rasteri/HIDman/firmware/usbll.c

#include <stdio.h>
#include <stdlib.h>
#include "type.h"
#include "ch559.h"
#include "system.h"
#include "defs.h"
#include "usbdef.h"
#include "usbhost.h"
#include "menu.h"
#include "data.h"
#include "settings.h"
#include "andyalloc.h"
#include "keyboardled.h"
#include "parsedescriptor.h"
#include "ps2protocol.h"
#include "usbll.h"

__at(0x0000) unsigned char __xdata RxBuffer[MAX_PACKET_SIZE];
__at(0x0100) unsigned char __xdata TxBuffer[MAX_PACKET_SIZE];

//root hub port
//USB_HUB_PORT __xdata RootHubPort[ROOT_HUB_PORT_NUM];

//sub hub port - should be dynamically allocated
//USB_HUB_PORT __xdata SubHubPort[ROOT_HUB_PORT_NUM][MAX_EXHUB_PORT_NUM];

__xdata LinkedList* PolledDevices = NULL;

UINT8 EnableRootHubPort(UINT8 rootHubIndex, UINT8 * DeviceSpeed)
{
	if (rootHubIndex == 0)
	{
		if (USB_HUB_ST & bUHS_H0_ATTACH)
		{
			if ((UHUB0_CTRL & bUH_PORT_EN) == 0x00)
			{
				if (USB_HUB_ST & bUHS_DM_LEVEL)
				{
					*DeviceSpeed = LOW_SPEED;

					TRACE("low speed device on hub 0\r\n");
				}
				else
				{
					*DeviceSpeed = FULL_SPEED;

					TRACE("full speed device on hub 0\r\n");
				}

				if (*DeviceSpeed == LOW_SPEED)
				{
					UHUB0_CTRL |= bUH_LOW_SPEED;
				}
			}

			UHUB0_CTRL |= bUH_PORT_EN;

			return ERR_SUCCESS;
		}
	}
	else if (rootHubIndex == 1)
	{
		if (USB_HUB_ST & bUHS_H1_ATTACH)
		{
			if ((UHUB1_CTRL & bUH_PORT_EN) == 0x00)
			{
				if (USB_HUB_ST & bUHS_HM_LEVEL)
				{
					*DeviceSpeed = LOW_SPEED;

					TRACE("low speed device on hub 1\r\n");
				}
				else
				{
					*DeviceSpeed = FULL_SPEED;

					TRACE("full speed device on hub 1\r\n");
				}

				if (*DeviceSpeed == LOW_SPEED)
				{
					UHUB1_CTRL |= bUH_LOW_SPEED;
				}
			}

			UHUB1_CTRL |= bUH_PORT_EN;

			return ERR_SUCCESS;
		}
	}

	return ERR_USB_DISCON;
}

void DisableRootHubPort(UINT8 RootHubIndex)
{

	if (RootHubIndex == 0)
	{
		UHUB0_CTRL = 0x00;
	}
	else if (RootHubIndex == 1)
	{
		UHUB1_CTRL = 0x00;
	}
}



void SetHostUsbAddr(UINT8 addr)
{
	USB_DEV_AD = USB_DEV_AD & bUDA_GP_BIT | addr & 0x7F;
}

void SetUsbSpeed(UINT8 FullSpeed) // set current speed
{
	if (FullSpeed)
	{
		USB_CTRL &= ~bUC_LOW_SPEED;
		UH_SETUP &= ~bUH_PRE_PID_EN;
	}
	else
	{
		USB_CTRL |= bUC_LOW_SPEED;
	}
}

void ResetRootHubPort(UINT8 RootHubIndex)
{
	SetHostUsbAddr(0x00);
	SetUsbSpeed(1);

	if (RootHubIndex == 0)
	{
		UHUB0_CTRL = UHUB0_CTRL & ~bUH_LOW_SPEED | bUH_BUS_RESET; 
		mDelaymS(25);											  
		UHUB0_CTRL = UHUB0_CTRL & ~bUH_BUS_RESET;				  
	}
	else if (RootHubIndex == 1)
	{
		UHUB1_CTRL = UHUB1_CTRL & ~bUH_LOW_SPEED | bUH_BUS_RESET; 
		mDelaymS(25);											  
		UHUB1_CTRL = UHUB1_CTRL & ~bUH_BUS_RESET;				  
	}

	mDelayuS(250);
	UIF_DETECT = 0;
}

void SelectHubPort(USB_HUB_PORT *pUsbDevice)
{
	if (pUsbDevice->IsRootHub)
	{
		// normal device
		SetHostUsbAddr(pUsbDevice->DeviceAddress);
		SetUsbSpeed(pUsbDevice->DeviceSpeed);
	}
	else
	{
		SetHostUsbAddr(pUsbDevice->DeviceAddress);
		if (pUsbDevice->DeviceSpeed == LOW_SPEED)
		{
			UH_SETUP |= bUH_PRE_PID_EN;
		}
		SetUsbSpeed(pUsbDevice->DeviceSpeed);
	}
}

/*void SelectHubPort(UINT8 RootHubIndex, UINT8 HubPortIndex)
{
	if (HubPortIndex == EXHUB_PORT_NONE)
	{
		//normal device
		SetHostUsbAddr(RootHubPort[RootHubIndex].DeviceAddress);
		SetUsbSpeed(RootHubPort[RootHubIndex].DeviceSpeed);
	}
	else
	{
		USB_HUB_PORT *pUsbDevice = &SubHubPort[RootHubIndex][HubPortIndex];
		SetHostUsbAddr(pUsbDevice->DeviceAddress);
		if (pUsbDevice->DeviceSpeed == LOW_SPEED)
		{
			UH_SETUP |= bUH_PRE_PID_EN;
		}

		SetUsbSpeed(pUsbDevice->DeviceSpeed);
	}
}*/

void InitUsbHost(void)
{
	UINT8 i;
	IE_USB = 0;

	USB_CTRL = bUC_HOST_MODE;
	USB_DEV_AD = 0x00;
	UH_EP_MOD = bUH_EP_TX_EN | bUH_EP_RX_EN;
	UH_RX_DMA = 0x0000;
	UH_TX_DMA = 0x0001;
	UH_RX_CTRL = 0x00;
	UH_TX_CTRL = 0x00;

	UHUB1_CTRL &= ~bUH1_DISABLE; //enable root hub1

	USB_CTRL = bUC_HOST_MODE | bUC_INT_BUSY | bUC_DMA_EN;

	UH_SETUP = bUH_SOF_EN;
	USB_INT_FG = 0xFF;
	for (i = 0; i < 2; i++)
	{
		DisableRootHubPort(i);
	}
	USB_INT_EN = bUIE_TRANSFER | bUIE_DETECT;
}

UINT8   USBHostTransact( UINT8 endp_pid, UINT8 tog, UINT16 timeout )
{
    UINT8   TransRetry;
    UINT8   s, r;
    UINT16  i;
    UH_RX_CTRL = tog;
    UH_TX_CTRL =tog ;
    TransRetry = 0;
    do
    {
        UH_EP_PID = endp_pid;                                    // 指定令牌PID和目的端点号
        UIF_TRANSFER = 0;                                        // 允许传输

        for ( i = WAIT_USB_TOUT_200US; i != 0 && UIF_TRANSFER == 0; i -- )
        {
            ;
        }
        UH_EP_PID = 0x00;                                        // 停止USB传输

        if ( UIF_TRANSFER == 0 )
        {
            return( ERR_USB_UNKNOWN );
        }

        if ( UIF_TRANSFER )                                      // 传输完成
        {
            if ( U_TOG_OK )
            {
                return( ERR_SUCCESS );
            }
            r = USB_INT_ST & MASK_UIS_H_RES;                     // USB设备应答状态
            if ( r == USB_PID_STALL )
            {
                //printf("USB_PID_STALL\n");
                return( r | ERR_USB_TRANSFER );
            }
            if ( r == USB_PID_NAK )
            {
                if ( timeout == 0 )
                {
                    //printf("USB_PID_NAK timeout\n");
                    return( r | ERR_USB_TRANSFER );
                }
                if ( timeout < 0xFFFF )
                {
                    timeout --;
                }
                -- TransRetry;
            }
            else switch ( endp_pid >> 4 )
                {
                case USB_PID_SETUP:
                case USB_PID_OUT:
                    if ( U_TOG_OK )
                    {
                        return( ERR_SUCCESS );
                    }
                    if ( r == USB_PID_ACK )
                    {
                        return( ERR_SUCCESS );
                    }
                    if ( r == USB_PID_STALL || r == USB_PID_NAK )
                    {
                        //printf("USB PID OUT : USB_PID_STALL or USB_PID_NAK timeout %x\n", r);
                        return( r | ERR_USB_TRANSFER );
                    }
                    if ( r )
                    {
                        //printf("USB PID OUT : ERR_USB_TRANSFER unexpected answer %x\n", r);
                        return( r | ERR_USB_TRANSFER );          // Not a timeout/error, unexpected answer
                    }
                    break;                                       // 超时重试
                case USB_PID_IN:
                    if ( U_TOG_OK )
                    {
                        return( ERR_SUCCESS );
                    }
                    if ( tog ? r == USB_PID_DATA1 : r == USB_PID_DATA0 )
                    {
                        return( ERR_SUCCESS );
                    }
                    if ( r == USB_PID_STALL || r == USB_PID_NAK )
                    {
                        //printf("USB_PID_IN : USB_PID_STALL or USB_PID_NAK%x\n", r);
                        return( r | ERR_USB_TRANSFER );
                    }
                    if ( r == USB_PID_DATA0 && r == USB_PID_DATA1 )// 不同步则需丢弃后重试
                    {
                    }                                            // 不同步重试
                    else if ( r )
                    {
                        //printf("USB_PID_IN : ERR_USB_TRANSFER unexpected answer %x\n", r);
                        return( r | ERR_USB_TRANSFER );          // 不是超时/出错,意外应答
                    }
                    break;                                       // 超时重试
                default:
                    //printf("unknown err\n");
                    return( ERR_USB_UNKNOWN );                   // 不可能的情况
                    break;
                }
        }
        else                                                     // 其它中断,不应该发生的情况
        {
            USB_INT_FG = 0xFF;                                   //清中断标志
        }
        mDelayuS( 15 );
    }
    while ( ++ TransRetry < 3 );
    return( ERR_USB_TRANSFER );                                  // 应答超时
}


UINT8 HostCtrlTransfer(USB_SETUP_REQ *pSetupReq, UINT8 MaxPacketSize0, PUINT8 DataBuf, PUINT16 RetLen)
{
	UINT16 RemLen = 0;
	UINT8 s, RxLen, RxCnt, TxCnt;
	PUINT8 pBuf;
	PUINT16 pLen;

	pBuf = DataBuf;
	pLen = RetLen;
	mDelayuS(200);
	if (pLen)
	{
		*pLen = 0;
	}

	for (TxCnt = 0; TxCnt < sizeof(USB_SETUP_REQ); TxCnt++)
	{
		TxBuffer[TxCnt] = ((UINT8 *)pSetupReq)[TxCnt];
	}

	UH_TX_LEN = sizeof(USB_SETUP_REQ);

	s = USBHostTransact(USB_PID_SETUP << 4, 0x00, 10000);
	if (s != ERR_SUCCESS)
	{
		TRACE1("quit at line %d\r\n", (UINT16)__LINE__);

		return (s);
	}
	UH_RX_CTRL = UH_TX_CTRL = bUH_R_TOG | bUH_R_AUTO_TOG | bUH_T_TOG | bUH_T_AUTO_TOG;
	UH_TX_LEN = 0x01;
	RemLen = (pSetupReq->wLengthH << 8) | (pSetupReq->wLengthL);
	if (RemLen && pBuf)
	{
		if (pSetupReq->bRequestType & USB_REQ_TYP_IN)
		{
			while (RemLen)
			{
				mDelayuS(200);
				s = USBHostTransact(USB_PID_IN << 4, UH_RX_CTRL, 10000);
				if (s != ERR_SUCCESS)
				{
					TRACE1("quit at line %d\r\n", (UINT16)__LINE__);

					return (s);
				}
				RxLen = USB_RX_LEN < RemLen ? USB_RX_LEN : RemLen;
				RemLen -= RxLen;
				if (pLen)
				{
					*pLen += RxLen;
				}

				for (RxCnt = 0; RxCnt != RxLen; RxCnt++)
				{
					*pBuf = RxBuffer[RxCnt];
					pBuf++;
				}
				if (USB_RX_LEN == 0 || (USB_RX_LEN < MaxPacketSize0))
				{
					break;
				}
			}
			UH_TX_LEN = 0x00;
		}
		else
		{
			while (RemLen)
			{
				mDelayuS(200);
				UH_TX_LEN = RemLen >= MaxPacketSize0 ? MaxPacketSize0 : RemLen;

				for (TxCnt = 0; TxCnt != UH_TX_LEN; TxCnt++)
				{
					TxBuffer[TxCnt] = *pBuf;
					pBuf++;
				}
				s = USBHostTransact(USB_PID_OUT << 4 | 0x00, UH_TX_CTRL, 200000 / 20);
				if (s != ERR_SUCCESS)
				{
					TRACE1("quit at line %d\r\n", (UINT16)__LINE__);

					return (s);
				}
				RemLen -= UH_TX_LEN;
				if (pLen)
				{
					*pLen += UH_TX_LEN;
				}
			}


		}
	}

	mDelayuS(200);
	s = USBHostTransact((UH_TX_LEN ? USB_PID_IN << 4 | 0x00 : USB_PID_OUT << 4 | 0x00), bUH_R_TOG | bUH_T_TOG, 200000 / 20);
	if (s != ERR_SUCCESS)
	{
		TRACE1("quit at line %d\r\n", (UINT16)__LINE__);

		return (s);
	}
	if (UH_TX_LEN == 0)
	{
		return (ERR_SUCCESS); // ״̬OUT
	}
	if (USB_RX_LEN == 0)
	{
		return (ERR_SUCCESS);
	}
	return (ERR_USB_BUF_OVER);
}

UINT8 TransferReceive(ENDPOINT *pEndPoint, UINT8 *pData, UINT16 *pRetLen, UINT16 timeout)
{
	UINT8 s;
	UINT8 len;

	s = USBHostTransact(USB_PID_IN << 4 | (pEndPoint->EndpointAddr & 0x7F), pEndPoint->TOG ? bUH_R_TOG | bUH_T_TOG : 0, timeout);
	if (s == ERR_SUCCESS)
	{
		UINT8 i;
		len = USB_RX_LEN;

		for (i = 0; i < len; i++)
		{
			*pData++ = RxBuffer[i];
		}

		if (pRetLen != NULL)
		{
			*pRetLen = len;
		}

		pEndPoint->TOG = pEndPoint->TOG ? FALSE : TRUE;
	}

	return (s);
}

UINT8 TransferSend(ENDPOINT *pEndPoint, UINT8 *pData, UINT8 len, UINT16 timeout)
{
	UINT8 s;
	UINT8 i;

	// Copy data to transmit buffer
	for (i = 0; i < len; i++)
	{
		TxBuffer[i] = pData[i];
	}
	UH_TX_LEN = len;

	s = USBHostTransact(USB_PID_OUT << 4 | (pEndPoint->EndpointAddr & 0x7F), pEndPoint->TOG ? bUH_R_TOG | bUH_T_TOG : 0, timeout);
	if (s == ERR_SUCCESS)
	{
		pEndPoint->TOG = pEndPoint->TOG ? FALSE : TRUE;
	}

	return (s);
}
