rasteri/HIDman/firmware/inc/usbhost.h

#ifndef _USBHOST_H_
#define _USBHOST_H_

#include <stdbool.h>
#include "defs.h"
#include "linkedlist.h"


#define ERR_SUCCESS         0x00
#define ERR_USB_CONNECT     0x15
#define ERR_USB_DISCON      0x16
#define ERR_USB_BUF_OVER    0x17
#define ERR_USB_DISK_ERR    0x1F
#define ERR_USB_TRANSFER    0x20
#define ERR_USB_UNSUPPORT   0xFB
#define ERR_USB_UNKNOWN     0xFE





#ifndef	USB_INT_RET_ACK
#define	USB_INT_RET_ACK		     USB_PID_ACK
#define	USB_INT_RET_NAK		     USB_PID_NAK
#define	USB_INT_RET_STALL	     USB_PID_STALL
#define	USB_INT_RET_DATA0	     USB_PID_DATA0
#define	USB_INT_RET_DATA1	     USB_PID_DATA1
#define	USB_INT_RET_TOUT	     0x00
#define	USB_INT_RET_TOUT1	     0x04
#define	USB_INT_RET_TOUT2	     0x08
#define	USB_INT_RET_TOUT3	     0x0C
#endif

//number of root hub ports
#define ROOT_HUB_PORT_NUM      2

//maximum number of external hub ports
#define MAX_EXHUB_PORT_NUM     4

//none external hub port
#define EXHUB_PORT_NONE        0xff

//maximum number of interfaces per devicve
#define MAX_INTERFACE_NUM      4
//maximum number of interfaces across all devices
#define MAX_GLOBAL_INTERFACE_NUM      12
//maximum number of endpoints per interface
#define MAX_ENDPOINT_NUM       4
//maximum level of external hub
#define MAX_EXHUB_LEVEL        1

//in 
#define ENDPOINT_OUT           0
//out
#define ENDPOINT_IN            1

//endpoint struct
typedef struct _ENDPOINT
{
	UINT8 EndpointAddr;
	UINT16 MaxPacketSize;
	
	UINT8 EndpointDir : 1;
	UINT8 TOG : 1;
} ENDPOINT, *PENDPOINT;

//hid report define
#define HID_LOCAL_ITEM_TAG_USAGE         0x00

#define HID_GLOBAL_ITEM_TAG_USAGE_PAGE       0x00
#define HID_GLOBAL_ITEM_TAG_LOGICAL_MINIMUM  0x01
#define HID_GLOBAL_ITEM_TAG_LOGICAL_MAXIMUM  0x02
#define HID_GLOBAL_ITEM_TAG_PHYSICAL_MINIMUM 0x03
#define HID_GLOBAL_ITEM_TAG_PHYSICAL_MAXIMUM 0x04
#define HID_GLOBAL_ITEM_TAG_REPORT_SIZE      0x07
#define HID_GLOBAL_ITEM_TAG_REPORT_ID        0x08
#define HID_GLOBAL_ITEM_TAG_REPORT_COUNT     0x09

#define HID_MAIN_ITEM_TAG_INPUT          0x08

#define TYPE_MAIN         0
#define TYPE_GLOBAL       1
#define TYPE_LOCAL        2

#define HID_ITEM_FORMAT_SHORT      0
#define HID_ITEM_FORMAT_LONG       1

#define HID_ITEM_TAG_LONG          15

//usage page
#define USAGE_PAGE_NONE            0x00
#define USAGE_PAGE_GENERIC_DESKTOP 0x01
#define USAGE_PAGE_KEYBOARD        0x07
#define USAGE_PAGE_BUTTON          0x09

//usage
#define USAGE_NONE         0x00
#define USAGE_X            0x30
#define USAGE_Y            0x31
#define USAGE_WHEEL        0x38

extern UINT8 sInterfacePoolPos;

typedef struct _HID_ITEM_INFO
{
	unsigned int format;
	UINT8 size;
	UINT8 type;
	UINT8 tag;

	union
	{
		UINT8  u8;
		INT8   s8;
		UINT16 u16;
		INT16  s16;
		UINT32 u32;
		INT32  s32;

		const UINT8 *longdata;
	} value;
	
} HID_ITEM;


//hid segement define
#define HID_SEG_KEYBOARD_MODIFIER_INDEX  0
#define HID_SEG_KEYBOARD_VAL_INDEX       1

#define HID_SEG_BUTTON_INDEX             2
#define HID_SEG_X_INDEX                  3
#define HID_SEG_Y_INDEX                  4
#define HID_SEG_WHEEL_INDEX              5

#define HID_SEG_NUM                      6

#define MAX_USAGE_NUM      10

#define MAX_REPORTS 18

//interface struct
typedef struct _INTERFACE
{
	UINT8     InterfaceClass;
	UINT8	  InterfaceSubClass;
	UINT8     InterfaceProtocol;

	UINT16    ReportSize;
	
	UINT8     EndpointNum;   //number of endpoints in this interface
	ENDPOINT  Endpoint[MAX_ENDPOINT_NUM]; //endpoints
	
	bool usesReports;
	__xdata LinkedList *Reports;

} INTERFACE, *PINTERFACE;
void InitInterface(INTERFACE* Interface);

//hub struct
#define  PORT_DEVICE_NONE         0
#define  PORT_DEVICE_INSERT       1
#define  PORT_DEVICE_ENUM_FAILED  2
#define  PORT_DEVICE_ENUM_SUCCESS 3

// This is actually more like a "device on hub port" than a port itself
typedef struct _USB_HUB_PORT
{
	// Port status
	UINT8		HubPortStatus;
	UINT8       HubPortNum;

	// Device Status
	UINT8       DeviceClass;
	UINT8       MaxPacketSize0;
	
	UINT16      VendorID;
	UINT16      ProductID;
/* this isn't needed
	UINT16      bcdDevice;
*/

	UINT8       DeviceAddress;
	UINT8       DeviceSpeed;
	UINT8       InterfaceNum;

	__xdata LinkedList* Interfaces;
	
	//not sure we need this or the next one
	// which root hub this device is attached to
	UINT8		RootHubNum;

	// whether or not this device is directly connected to root
	UINT8		IsRootHub;

	// Logitech Fn swap configured successfully
	UINT8		LogitechConfigured;
	// keyboard sent a keypress (awake); config should run from the main loop, not the poll path
	UINT8		LogitechWoke;
	// Logitech device slot that has keyboard (1-6), 0 if unknown
	UINT8		LogitechDevNum;
	// Logitech FN_INVERSION feature index, 0 if not discovered
	UINT8		LogitechFnFeatureIndex;

} USB_HUB_PORT, *USB_PHUB_PORT;

#define  LOW_SPEED      0
#define  FULL_SPEED     1


extern void InitUsbHost(void);
extern void InitUsbData(void);
extern void DealUsbPort(void);
extern void InterruptProcessRootHubPort(UINT8 port_index);
extern void UpdateUsbKeyboardLed(UINT8 led);
extern INTERFACE* AllocInterface(UINT8 count);
void ReenumerateAllPorts(void);

// Apply the Logitech Fn-swap setting to connected Unifying keyboards in place
void ReapplyLogitechFnSwap(void);

void ProcessUsbHostPort(void);

extern __xdata  BOOL volatile s_CheckUsbPort0;
extern __xdata  BOOL volatile s_CheckUsbPort1;

// USB specific traces

#if 0
#include <stdio.h>
#define TRACE(x)  printf(x)
#define TRACE1(fmt, x)  printf(fmt, x)
#define TRACE2(fmt, x1, x2) printf(fmt, x1, x2)
#define TRACE3(fmt, x1, x2, x3) printf(fmt, x1, x2, x3)

#else
#define TRACE(x)  
#define TRACE1(fmt, x)  
#define TRACE2(fmt, x1, x2)
#define TRACE3(fmt, x1, x2, x3)
#endif

#endif
