rasteri/HIDman/firmware/xt.c

#include <stdint.h>
#include <stdbool.h>
#include <stdio.h>
#include <string.h>
#include "ch559.h"
#include "usbhost.h"
#include "uart.h"
#include "ps2.h"
#include "data.h"
#include "ps2protocol.h"
#include "defs.h"
#include "xt.h"
#include "scancode.h"

__xdata uint16_t ratelimit = 0;

__xdata uint8_t oldstate = 0;
void XTProcessPort(void)
{
	const uint8_t *chunk;
	static __data uint8_t sb;

	bool reEnter = 0;

	do
	{
		/*if (ports[PORT_KEY].state != oldstate)
		{
			printf("%hhd-%hhd\n", ports[PORT_KEY].state, ports[PORT_KEY].sendbit);
			oldstate = ports[PORT_KEY].state;
		}*/
		sb = ports[PORT_KEY].sendbit;
		reEnter = 0;

		// XT bit-bang state machine
		switch (ports[PORT_KEY].state)
		{
		case S_INIT:
			ports[PORT_KEY].state = S_IDLE;
			reEnter = 1;
			ports[PORT_KEY].sendbit = 0;
			WritePS2Clock(PORT_KEY, 1);
			break;

		case S_IDLE:
			// if host is not inhibiting (i.e. not pulling clock low)
			if (ReadPS2Clock(PORT_KEY))
			{
				if (ports[PORT_KEY].rateLimit > 0) ports[PORT_KEY].rateLimit--;

				//if ratelimiter is ok and buffer not empty
				if (ports[PORT_KEY].rateLimit == 0 && ports[PORT_KEY].sendBuffEnd != ports[PORT_KEY].sendBuffStart)
				{

					ports[PORT_KEY].rateLimit = XT_RATE_LIMIT;

					chunk = ports[PORT_KEY].sendBuff.chunky[ports[PORT_KEY].sendBuffStart];
					ports[PORT_KEY].data = chunk[ports[PORT_KEY].bytenum + 1];
					//DEBUG_OUT("Consuming %x %x %x %x\n", ports[PORT_KEY].sendBuffStart, ports[PORT_KEY].sendBuffEnd, chunk[0], ports[PORT_KEY].data);

					// if data line is already high, we can go straight to sending data
					if (ReadPS2Data(PORT_KEY))
					{

						// Go to S_SEND_CLOCK_LOW even though we're technically high, as this will make sure counters are right etc
						// we could just jump straight to S_SEND_CLOCK_FALLING but better to keep logic consistent
						ports[PORT_KEY].state = S_SEND_CLOCK_LOW;
						ports[PORT_KEY].recvbit = 0;
						//reEnter = 1;
					}
					// otherwise, have to send an RTS first
					else
					{
						// make clock line low, then wait for CTS (data high)
						WritePS2Clock(PORT_KEY, 0);
						ports[PORT_KEY].state = S_WAITING_CTS;
						ports[PORT_KEY].recvbit = 0;
					}
				}

				ports[PORT_KEY].resetCounter = 0;
			}

			// host is inhibiting (pulling clock low)
			// wait 20ms then send self-test byte
			else {
				ports[PORT_KEY].resetCounter++;
				if (ports[PORT_KEY].resetCounter == 1200){
					SimonSaysSendKeyboard(KEY_BATCOMPLETE);
				}
			}

			break;

		case S_WAITING_CTS:

			ports[PORT_KEY].recvbit++;

			// wait 112us before doing anything
			if (ports[PORT_KEY].recvbit >= 6)
			{
				if (ReadPS2Data(PORT_KEY))
				{
					ports[PORT_KEY].state = S_SEND_CLOCK_LOW;

					// reuse recvbit as counter
					ports[PORT_KEY].recvbit = 0;
				}
			}
			else
			{
				// timeout waiting for CTS after 250us, go back to idle
				if (ports[PORT_KEY].recvbit >= 16)
				{
					WritePS2Clock(PORT_KEY, 1);
					WritePS2Data(PORT_KEY, 1);
					ports[PORT_KEY].recvbit = 0;
					ports[PORT_KEY].resetCounter = 0;
					ports[PORT_KEY].state = S_IDLE;
				}
			}
			break;

		case S_SEND_CLOCK_LOW:
			// reuse recvbit as counter
			ports[PORT_KEY].recvbit++;

			// we want to set the data in the middle of the low cycle
			if (ports[PORT_KEY].recvbit == 2)
			{

				// bit 0 is start bit (high)
				if (sb == 0)
				{
					WritePS2Data(PORT_KEY, 1);
				}

				// bits 1-8 are data bits
				else if (sb > 0 && sb < 9)
				{
					// set current bit data
					WritePS2Data(PORT_KEY, ports[PORT_KEY].data & 0x01);

					// shift in preperation for next bit
					ports[PORT_KEY].data = ports[PORT_KEY].data >> 1;
				}

				ports[PORT_KEY].sendbit++;
				ports[PORT_KEY].state = S_SEND_CLOCK_RISE;
				ports[PORT_KEY].recvbit = 0;

				//make clock high
				WritePS2Clock(PORT_KEY, 1);
			}
			/*else
			{
				ports[PORT_KEY].state = S_SEND_CLOCK_RISE;
				ports[PORT_KEY].recvbit = 0;
			}*/
			break;

		case S_SEND_CLOCK_RISE:
			ports[PORT_KEY].recvbit++;

			// first time round, set clock high
			if (ports[PORT_KEY].recvbit == 1)
			{
				//make clock high
				WritePS2Clock(PORT_KEY, 1);
			}
			// wait 6 clock cycles (100us) before the next thing
			else if (ports[PORT_KEY].recvbit >= 2)
			{
				ports[PORT_KEY].state = S_SEND_CLOCK_HIGH;
			}

			break;

		case S_SEND_CLOCK_HIGH:

			// if final bit, move onto next byte
			if (sb == 10)
			{
				ports[PORT_KEY].sendbit = 0;

				// for keyboard get the next byte in the chunk
				chunk = ports[PORT_KEY].sendBuff.chunky[ports[PORT_KEY].sendBuffStart];

				ports[PORT_KEY].bytenum++;

				// if we've run out of bytes in this chunk
				if (ports[PORT_KEY].bytenum == chunk[0])
				{
					// move onto next chunk
					//DEBUG_OUT("Consumed %x %x\n", ports[PORT_KEY].sendBuffStart, ports[PORT_KEY].sendBuffEnd);
					ports[PORT_KEY].sendBuffStart = (ports[PORT_KEY].sendBuffStart + 1) & 0x3F;
					ports[PORT_KEY].bytenum = 0;
				}
				else
				{
					ports[PORT_KEY].data = chunk[ports[PORT_KEY].bytenum + 1];
				}

				// also need to set data line high
				WritePS2Data(PORT_KEY, 1);

				// give ourselves a little break between bytes
				ports[PORT_KEY].state = S_IDLE;
				ports[PORT_KEY].resetCounter = 0;
			}
			else
			{
				ports[PORT_KEY].state = S_SEND_CLOCK_FALL;
			}
			break;

		// data has been set, send falling edge of clock
		case S_SEND_CLOCK_FALL:

			WritePS2Clock(PORT_KEY, 0);
			ports[PORT_KEY].state = S_SEND_CLOCK_LOW;
			ports[PORT_KEY].recvbit = 0;
			break;
		}
	} while (reEnter);
}
