rasteri/HIDman/firmware/inc/scancode.h

#ifndef __SCANCODES_H__
#define __SCANCODES_H__
#include <stdbool.h>
#include <stdint.h>

extern __code uint8_t KEY_ACK[];
extern __code uint8_t KEY_BATCOMPLETE[];
extern __code uint8_t KEY_ID[];

extern __code uint8_t MOUSE_ACK[];
extern __code uint8_t MOUSE_BATCOMPLETE[];
extern __code uint8_t MOUSE_ID[];

extern __code uint8_t KEY_LEFT_BREAK[];
extern __code uint8_t KEY_RIGHT_BREAK[];
extern __code uint8_t KEY_UP_BREAK[];
extern __code uint8_t KEY_DOWN_BREAK[];

extern __code uint8_t KEY_LEFT_MAKE[];
extern __code uint8_t KEY_RIGHT_MAKE[];
extern __code uint8_t KEY_UP_MAKE[];
extern __code uint8_t KEY_DOWN_MAKE[];

extern __code uint8_t KEY_LCTRL_MAKE[];
extern __code uint8_t KEY_LALT_MAKE[];
extern __code uint8_t KEY_SPACE_MAKE[];
extern __code uint8_t KEY_ENTER_MAKE[];

extern __code uint8_t KEY_LCTRL_BREAK[];
extern __code uint8_t KEY_LALT_BREAK[];
extern __code uint8_t KEY_SPACE_BREAK[];
extern __code uint8_t KEY_ENTER_BREAK[];

extern __code uint8_t KEY_SCANCODE_2[];
extern __code uint8_t KEY_ECHO[];
extern __code uint8_t KEY_ERROR[];

extern __code uint8_t KEY_SET1_LSHIFT_MAKE[];
extern __code uint8_t KEY_SET1_LSHIFT_BREAK[];

extern __code uint8_t KEY_SET2_LSHIFT_MAKE[];
extern __code uint8_t KEY_SET2_LSHIFT_BREAK[];

extern __code uint8_t * __code HIDtoSET2_Make[];
extern __code uint8_t * __code HIDtoSET2_Break[];

extern __code uint8_t * __code HIDtoSET1_Make[];
extern __code uint8_t * __code HIDtoSET1_Break[];

extern __code uint8_t KEY_SET2_WWWREFRESH_MAKE[];
extern __code uint8_t KEY_SET2_WWWREFRESH_BREAK[];

#endif //__SCANCODES_H__
