rasteri/HIDman/firmware/andyalloc.c

/*
    andyalloc.c

    Trivial allocator that just chucks everything on a heap in order
    Can't free, all memory must be wiped and re-filled
*/

#include <stdio.h>
#include <stdlib.h>
#include "type.h"
#include "ch559.h"
#include "system.h"
#include "defs.h"
#include "usbdef.h"
#include "usbhost.h"
#include "andyalloc.h"

__xdata uint8_t MemPool[MEMPOOLMAXSIZE];
__xdata uint8_t *MemPoolPtr = MemPool;
__xdata uint8_t *tmp;

uint16_t MemoryUsed(void) {
    return MemPoolPtr - MemPool;
}

uint16_t MemoryFree(void) {
    return MEMPOOLMAXSIZE - MemoryUsed();
}

void __xdata *andyalloc(size_t size)
{
    // trigger a watchdog reset if we run out of memory
    if (MemoryFree() <= size) {
        DEBUGOUT("Memory Exhausted");
        ET0 = 0;
        while (1);
    }
    tmp = MemPoolPtr;
    MemPoolPtr += size;
    return tmp;
}

void andyclearmem(void)
{
    MemPoolPtr = MemPool;
}

void printhexval(uint8_t x){
    printf("sp %X\n", x);
}

void printstackpointer(void)
{
    uint8_t dumdum = 0;

    printhexval((uint8_t)&dumdum);
}
