rasteri/HIDman/firmware/inc/ps2mapping.h

#ifndef __PS2MAPPING_H__
#define __PS2MAPPING_H__

void CreateBitfieldMapping(INTERFACE *pHidSegStruct);
void CreateUsageMapping(INTERFACE *pHidSegStruct);
void CreateArrayMapping(INTERFACE *pHidSegStruct);

#endif
